Contrix/VUT_FIT_BP/documentation/obrazky-figures/esp8266.pdf

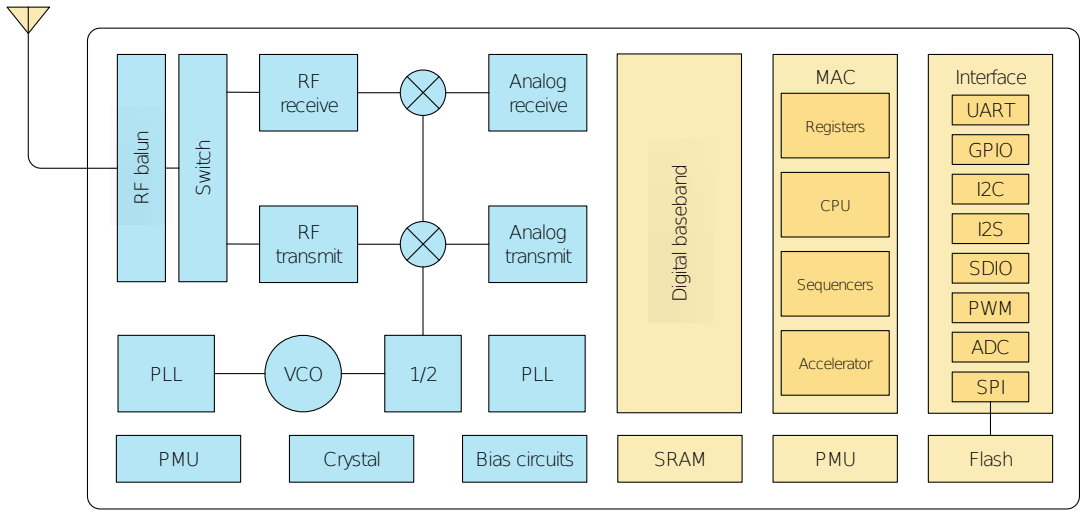
[picture p1: figure]
RF balun; Switch; RF receive; RF transmit; Analog receive; Analog transmit; PLL; VCO; Digital baseband; MAC; Interface; PMU; Crystal; Bias circuits; SRAM; SDIO; PWM; ADC; SPI; UART; GPIO; Flash; Registers; CPU; Sequencers; Accelerator
