Contrix/VUT_FIT_BP/documentation/obrazky-figures/cubemx.pdf

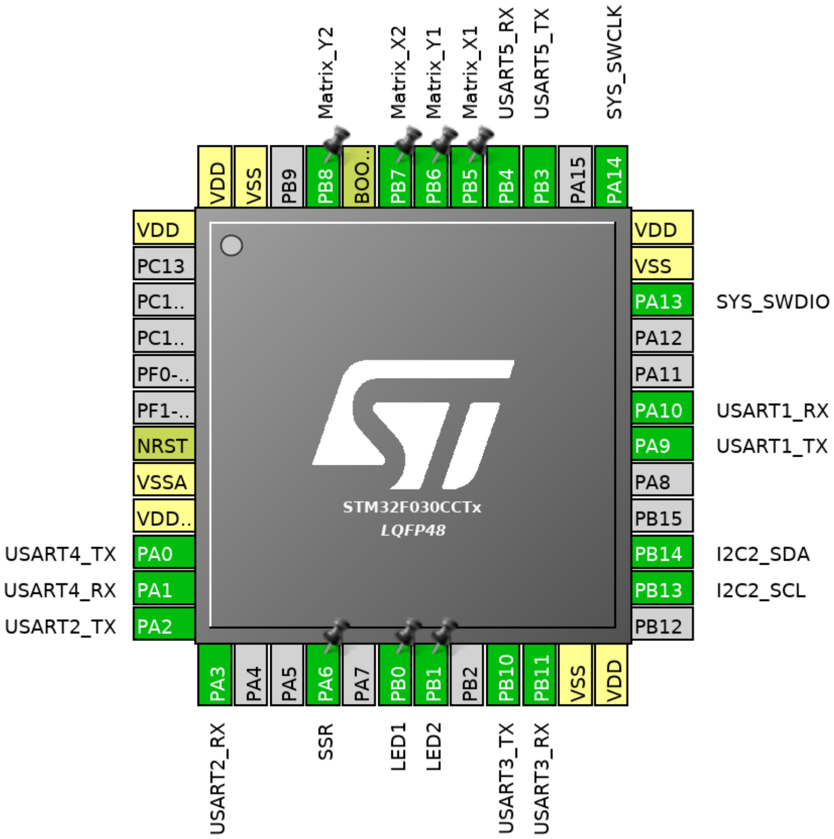
[picture p5: page 1]
