Contrix/VUT_FIT_BP/documentation/obrazky-figures/float.pdf

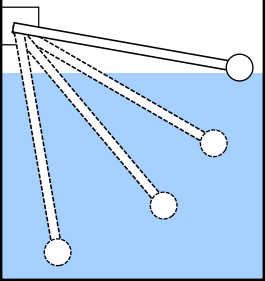
[picture p6: figure]
