Contrix/VUT_FIT_BP/documentation/obrazky-figures/jsn.pdf

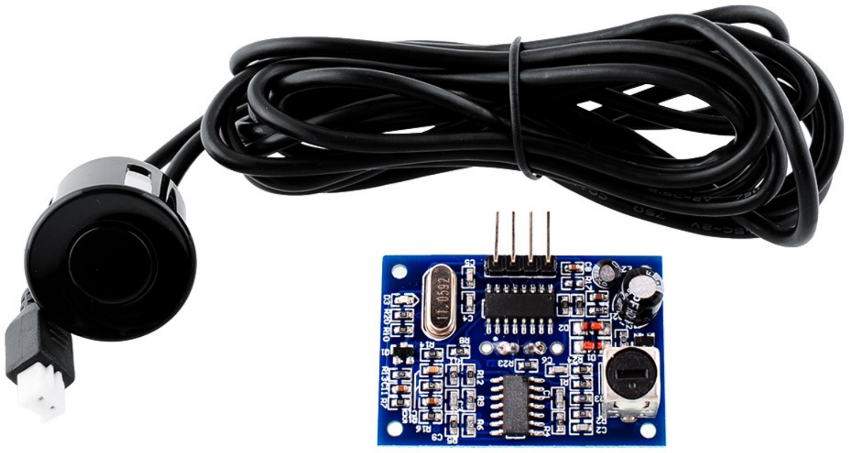
[picture p7: page 1]
