Contrix/VUT_FIT_BP/documentation/obrazky-figures/jsn_mes.pdf

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

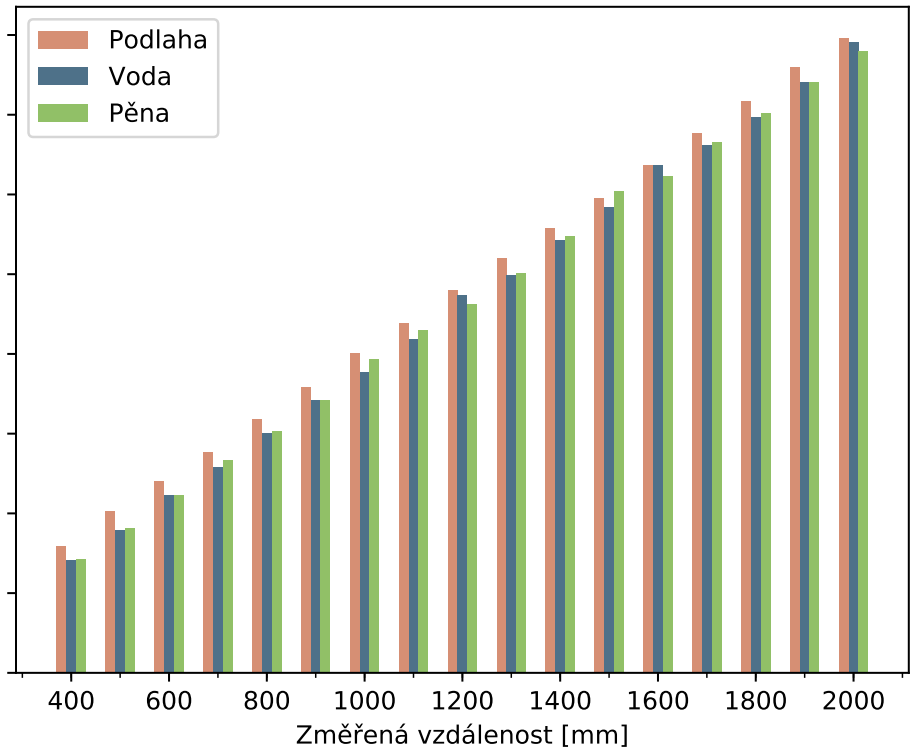
[picture p8: figure]
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
