Contrix/VUT_FIT_BP/documentation/obrazky-figures/lidar.pdf

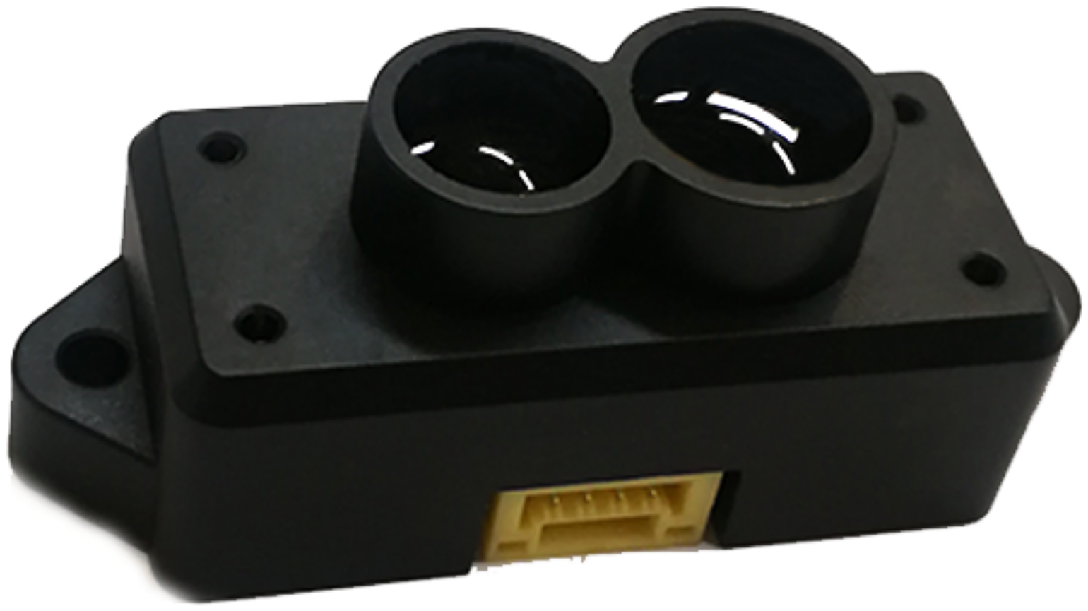
[picture p9: page 1]
