Contrix/VUT_FIT_BP/documentation/obrazky-figures/lidar_mes.pdf

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

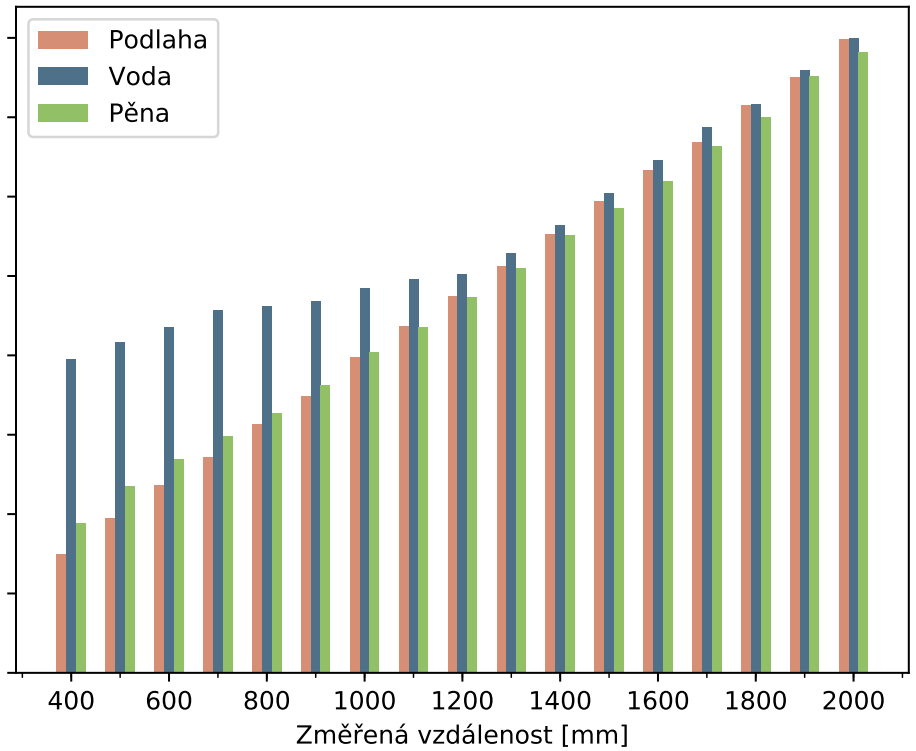
[picture p10: figure]
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
