Contrix/VUT_FIT_BP/documentation/obrazky-figures/main_board_3D.pdf

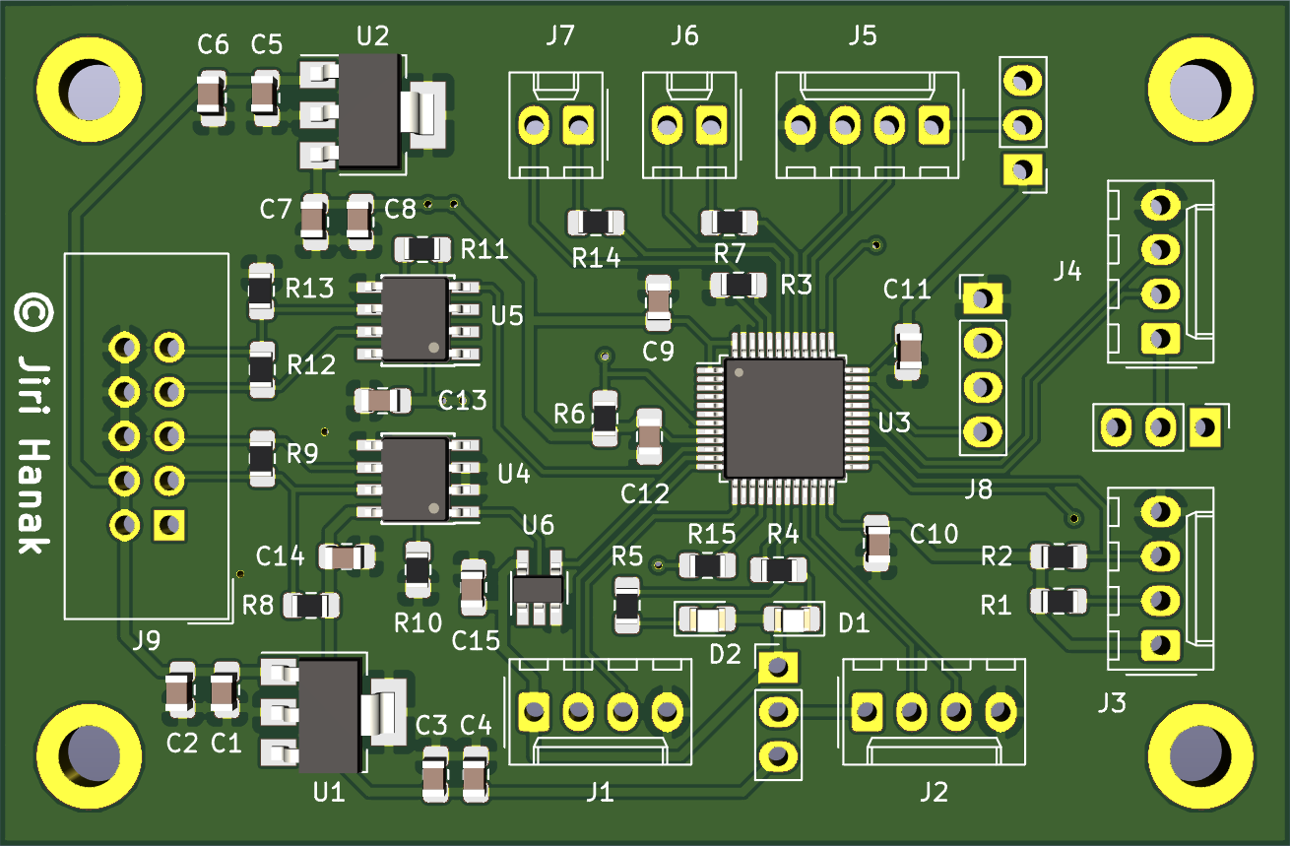
[picture p11: page 1]
