Contrix/VUT_FIT_BP/documentation/obrazky-figures/mcp.pdf

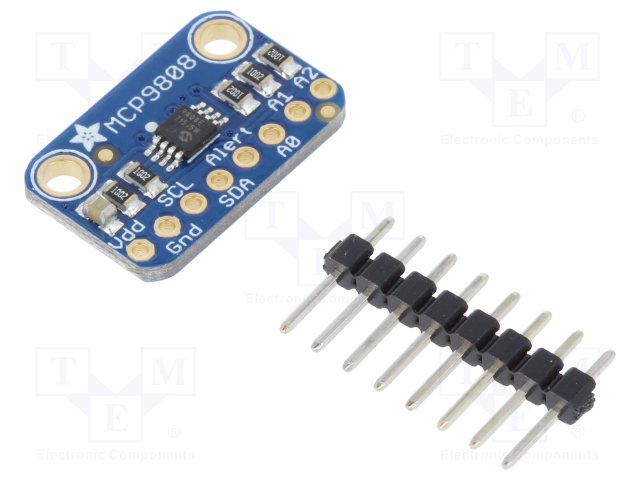
[picture p12: page 1]
