Contrix/VUT_FIT_BP/documentation/obrazky-figures/pk.pdf

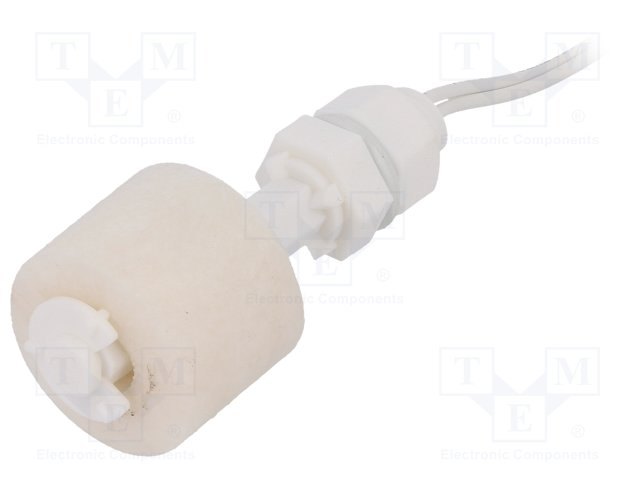
[picture p13: page 1]
