Contrix/VUT_FIT_BP/documentation/obrazky-figures/support_board_3D.pdf

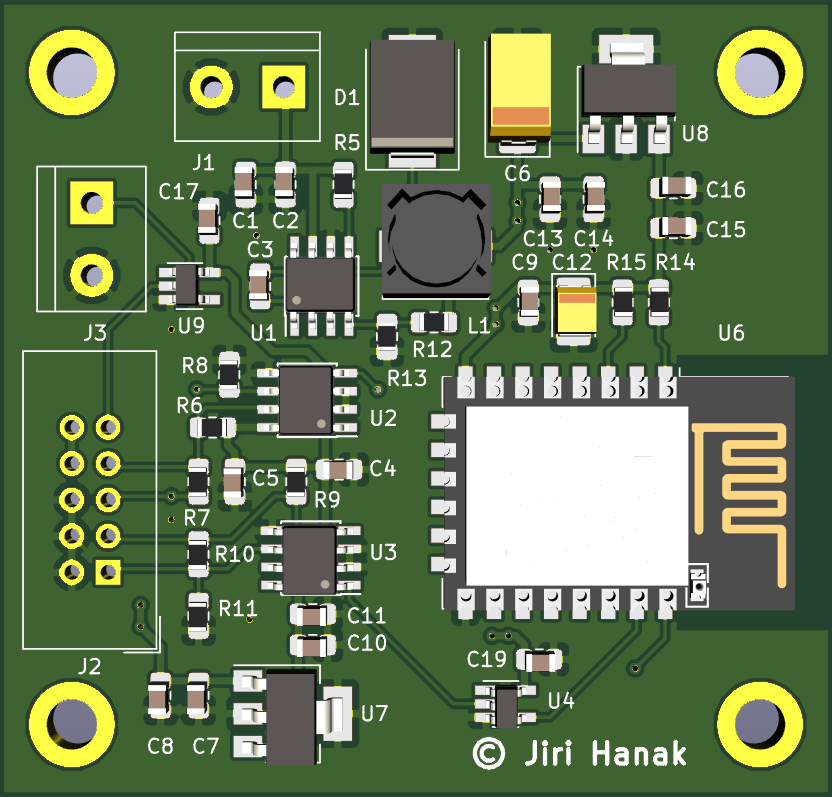
[picture p14: page 1]
