Contrix/VUT_FIT_BP/documentation/obrazky-figures/main_board_scheme.pdf

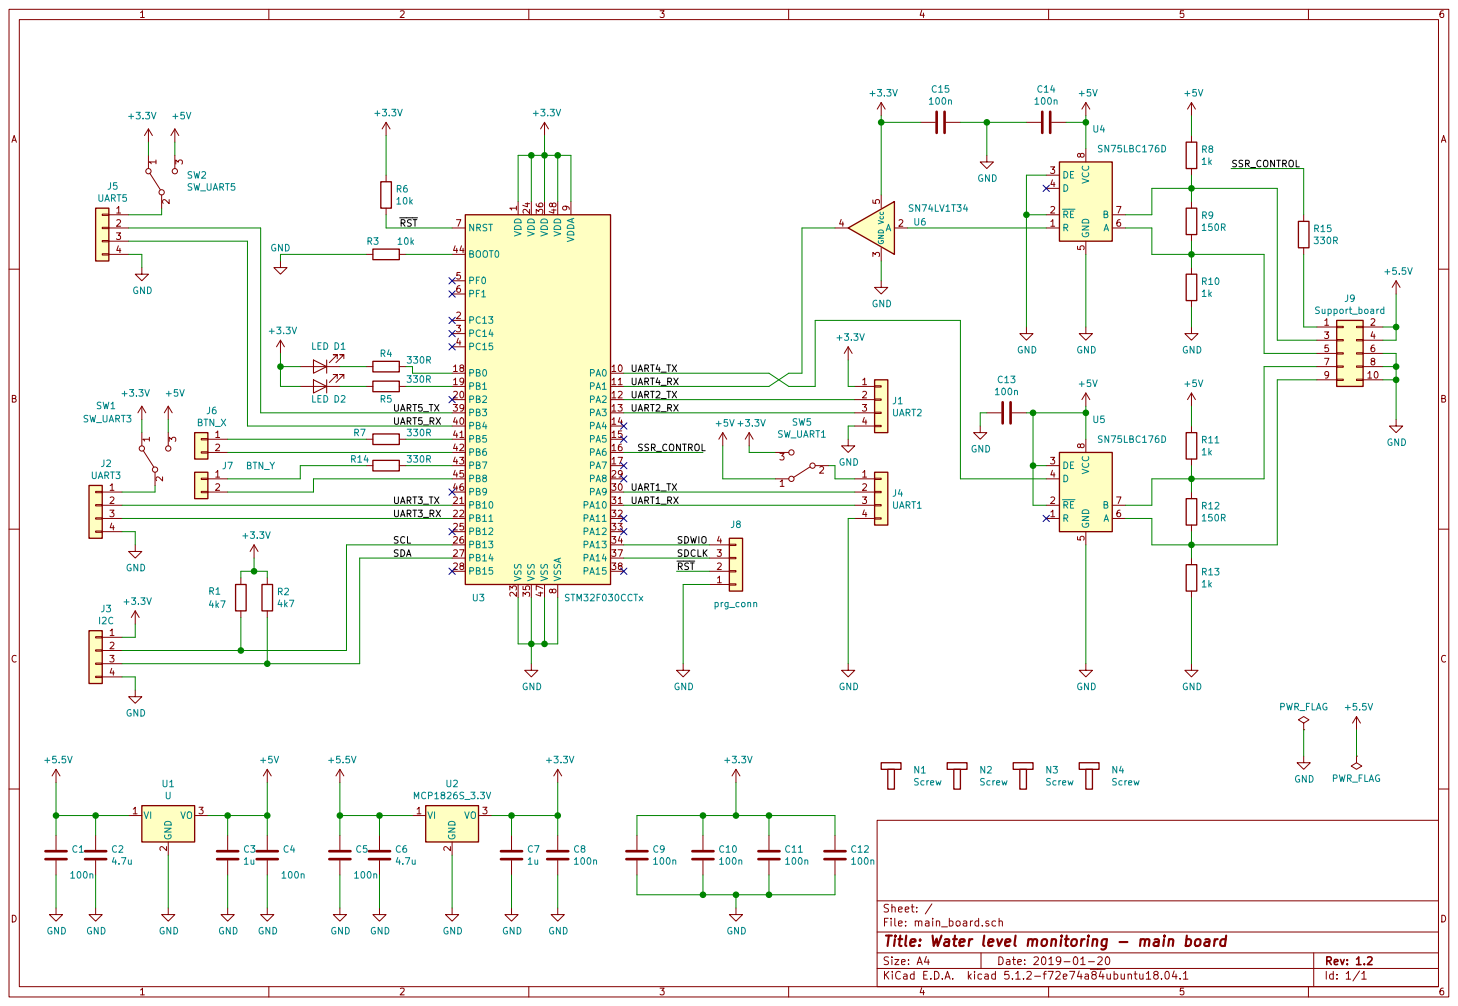
[picture p20: page 1]

1 VDD 24 VDD 36 VDD 48 VDDA

9 VSS 23 VSS 35 VSS 47 VSSA

File: main_board.sch Sheet: /
Id: 1/1 Title: Water level monitoring - main board
