Contrix/VUT_FIT_BP/documentation/obrazky-figures/support_board_scheme.pdf

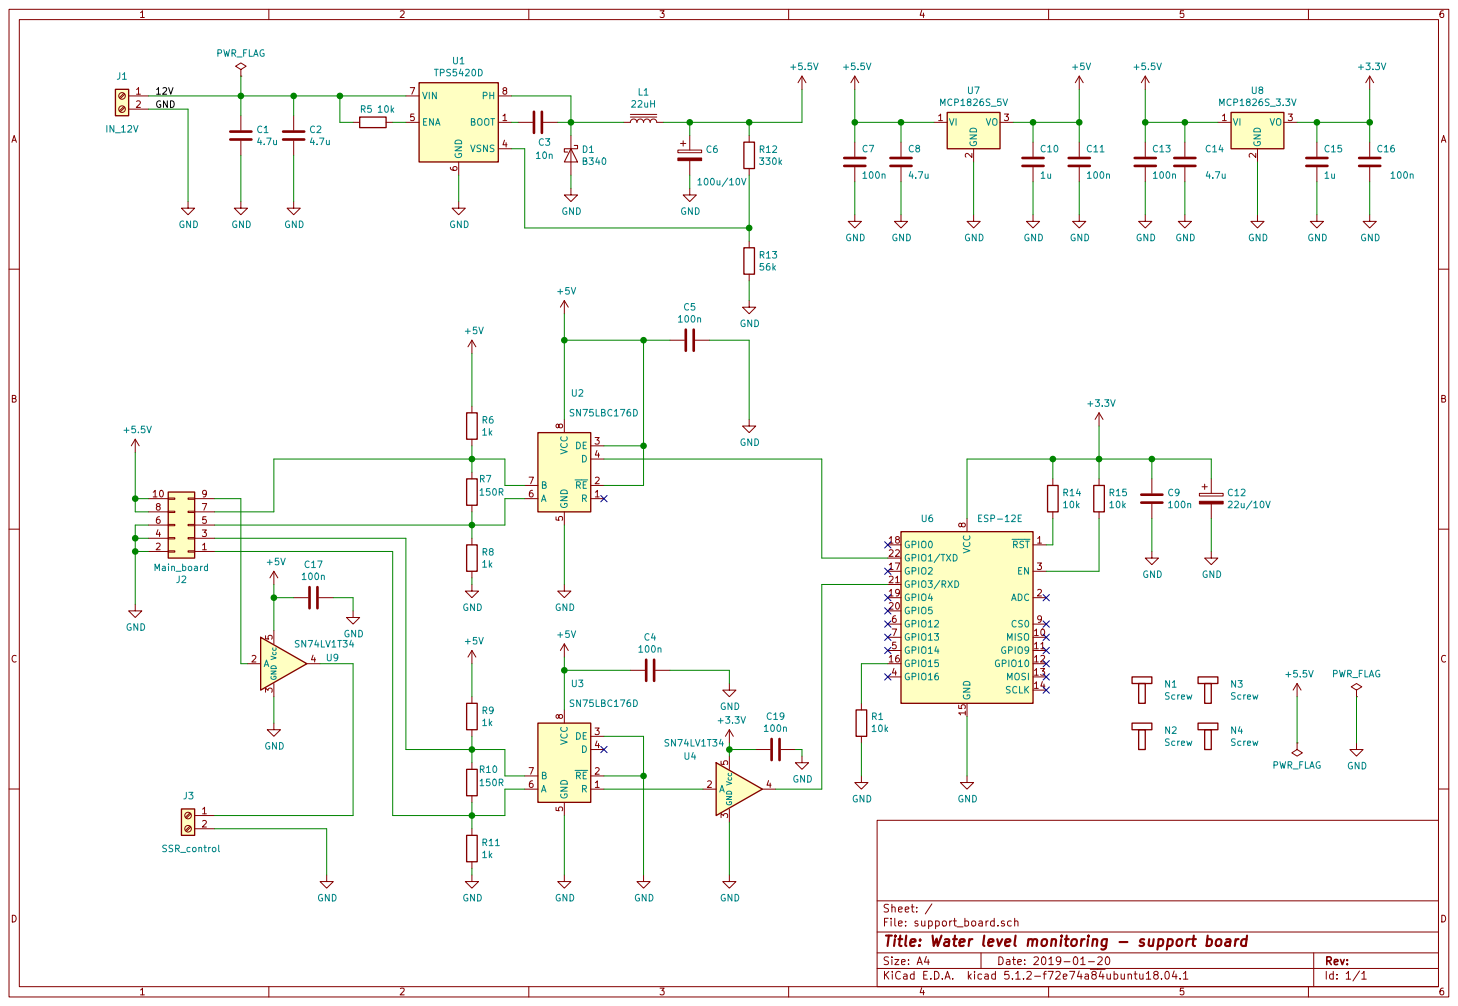
[picture p21: page 1]

6 VIN 7 PH 8 U1 TPS5420D GND GND
4.7u GND

File: support_board.sch Sheet: /
Id: 1/1 Title: Water level monitoring - support board
