Contrix/VUT_FIT_BP/documentation/obrazky-figures/diagram.pdf

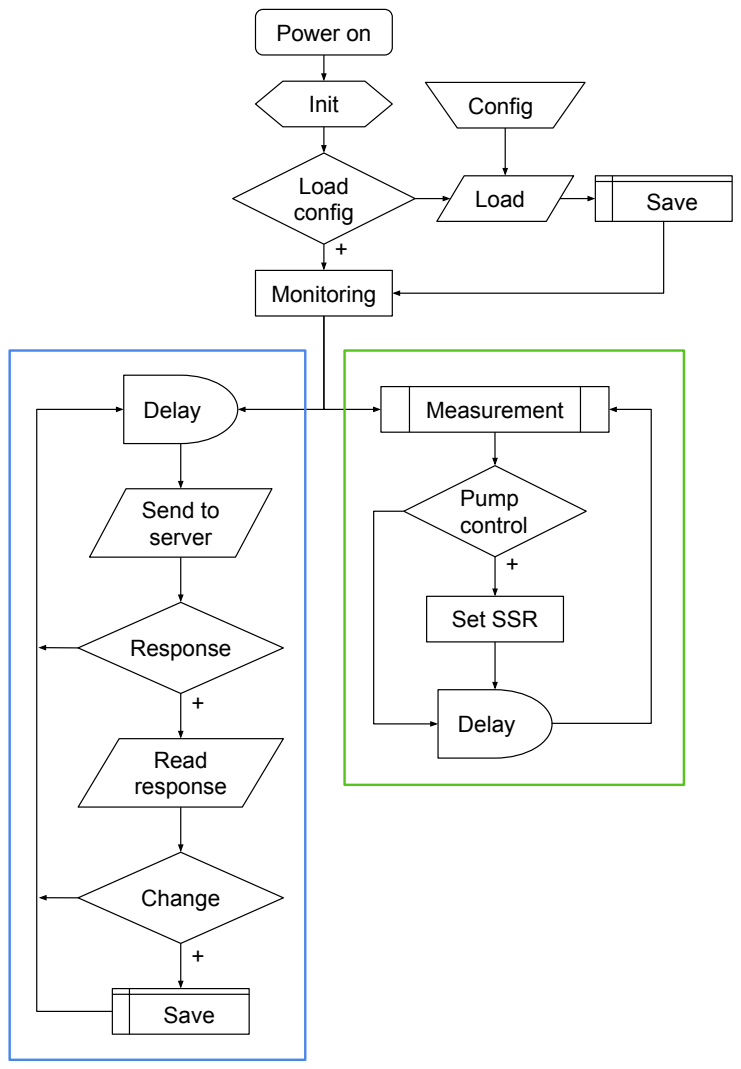
[picture p22: page 1]
Power on; Load config; Init; Load; Measurement; Save; Delay; Pump control; Send to server; Read response; Change; Monitoring; Set SSR; Config; Response
