Contrix/VUT_FIT_BP/documentation/obrazky-figures/scheme.pdf

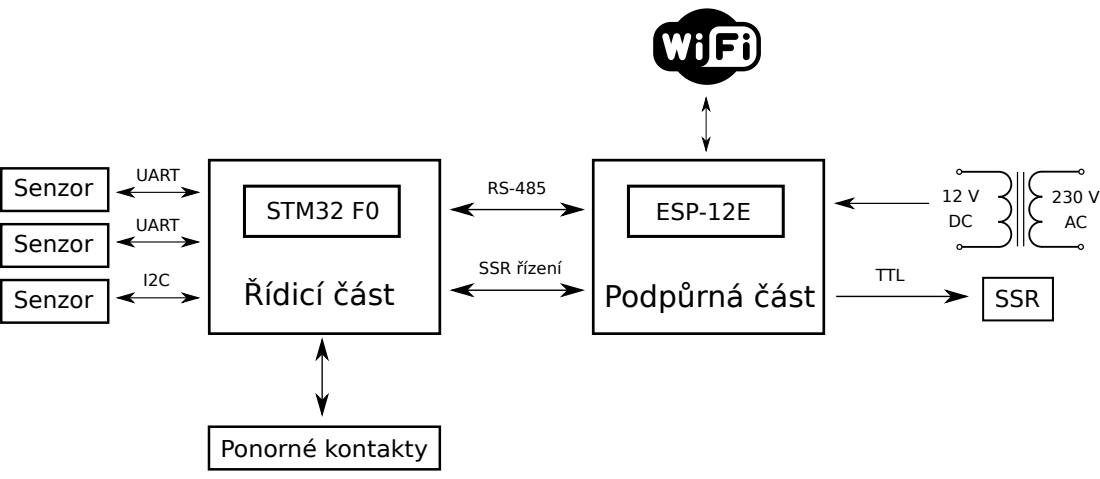
[picture p23: page 1]
Řídicí část; Podpůrná část; UART; Senzor; ESP-12E; 12 V DC STM32 F0; SSR; Ponorné kontakty

TTL SSR řízení
