Contrix/VUT_FIT_BP/hardware/support_board/gerber/support_board-F.Mask.pdf

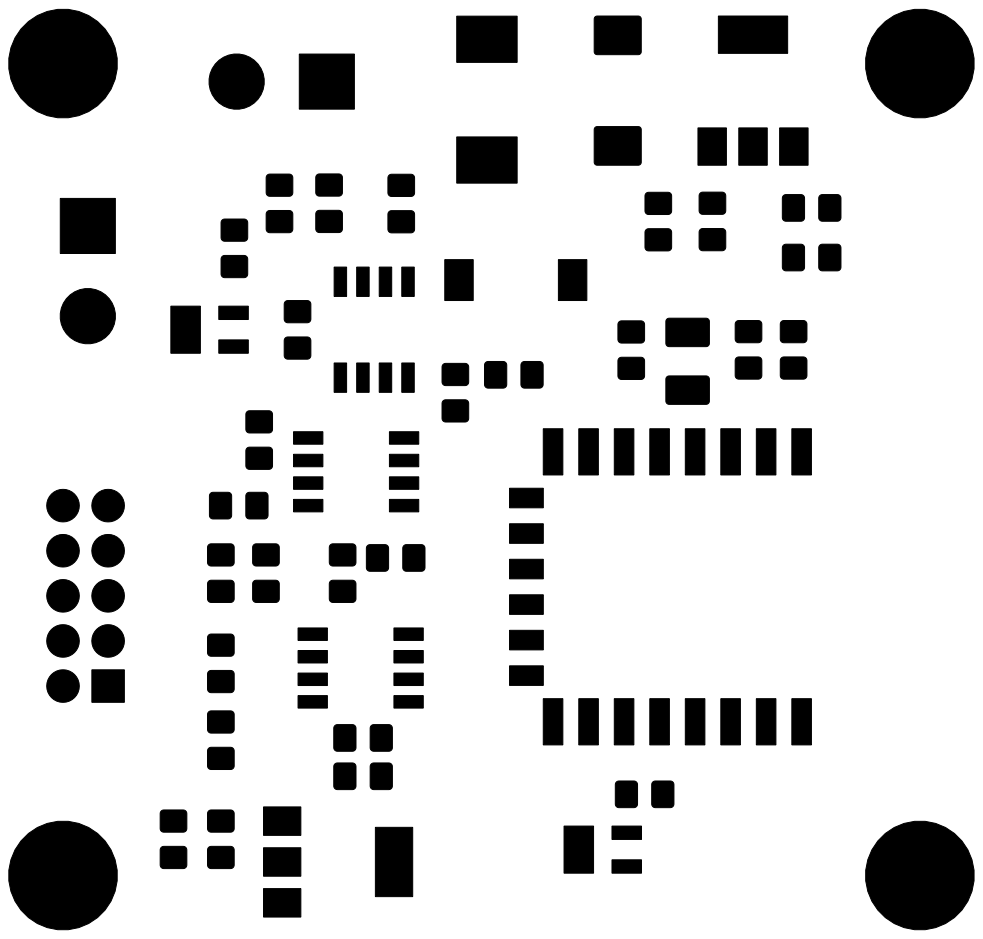
[picture p33: page 1]
