Contrix/VUT_FIT_BP/hardware/support_board/gerber/support_board-F.SilkS.pdf

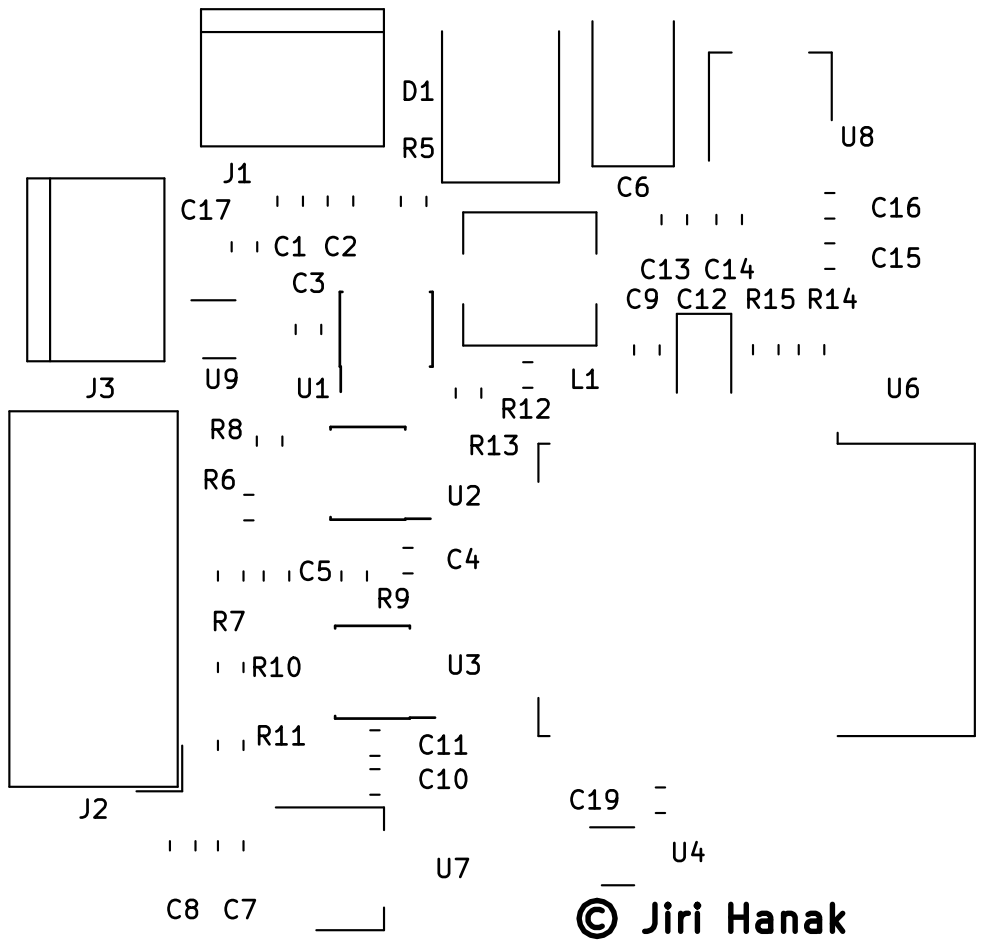
[picture p34: page 1]
