Contrix/VUT_FIT_BP/documentation/obrazky-figures/main_board_pcb.pdf

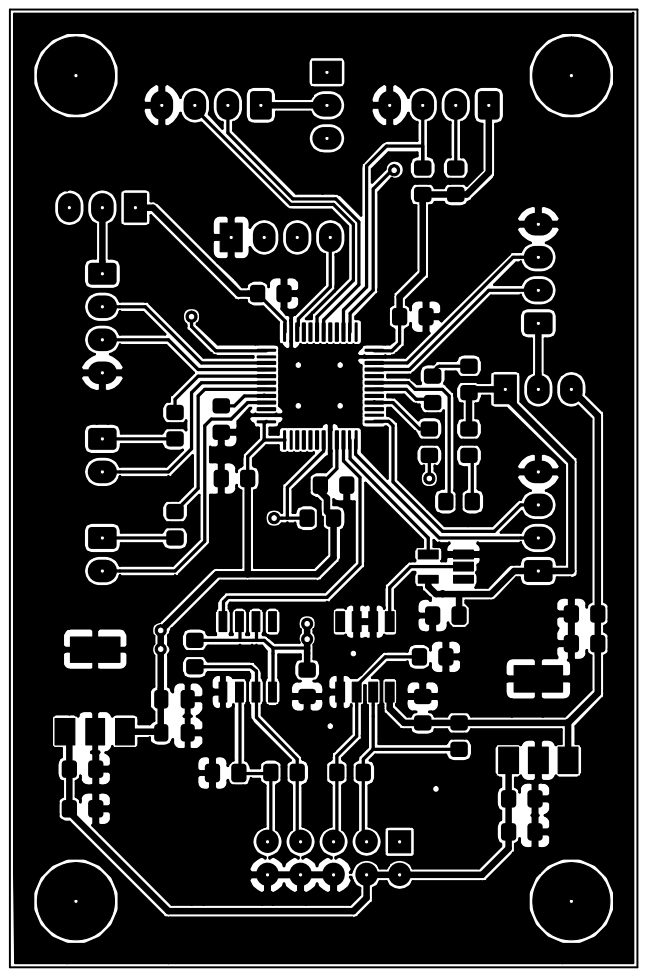
[picture p35: page 1]

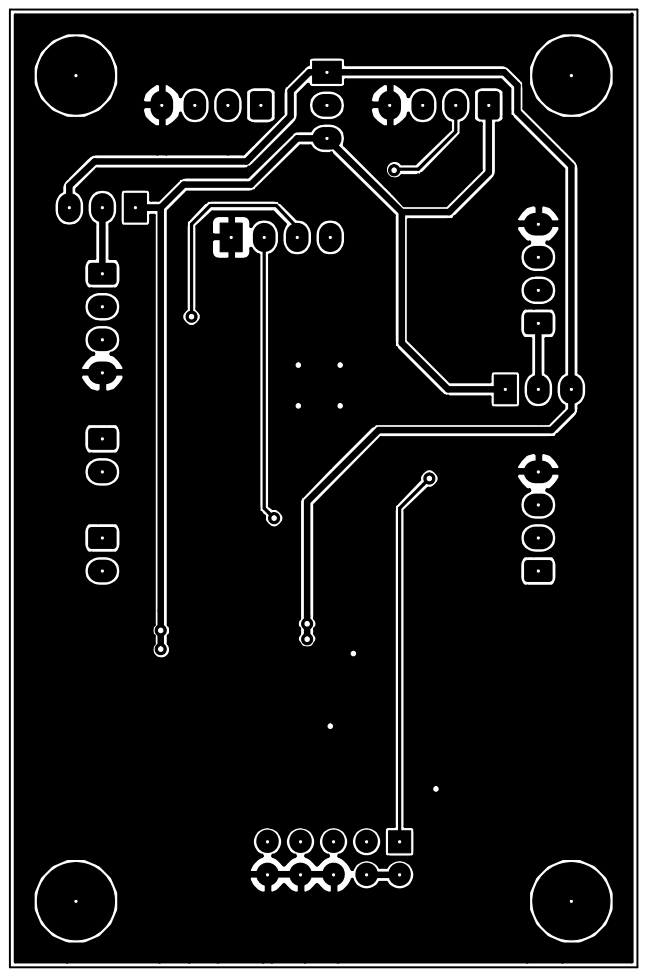
[picture p36: page 2]
