Contrix/VUT_FIT_BP/documentation/obrazky-figures/support_board_pcb.pdf

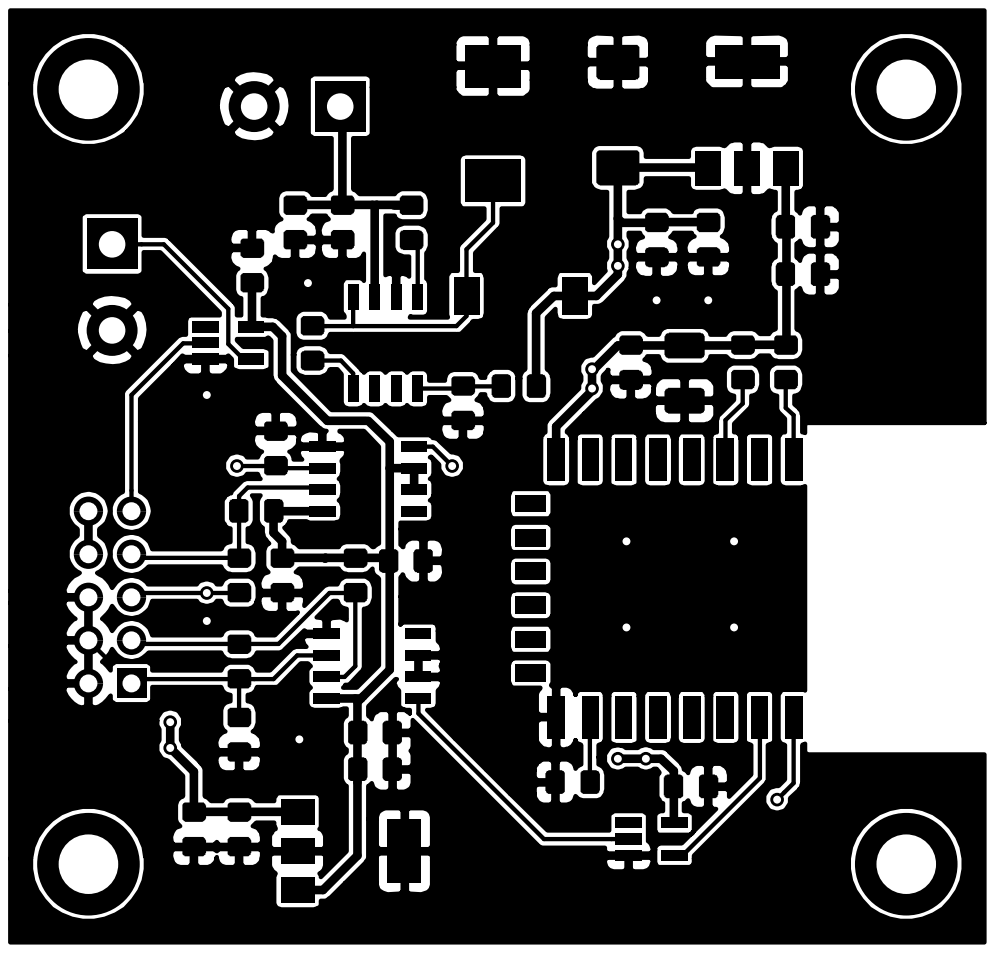
[picture p37: page 1]

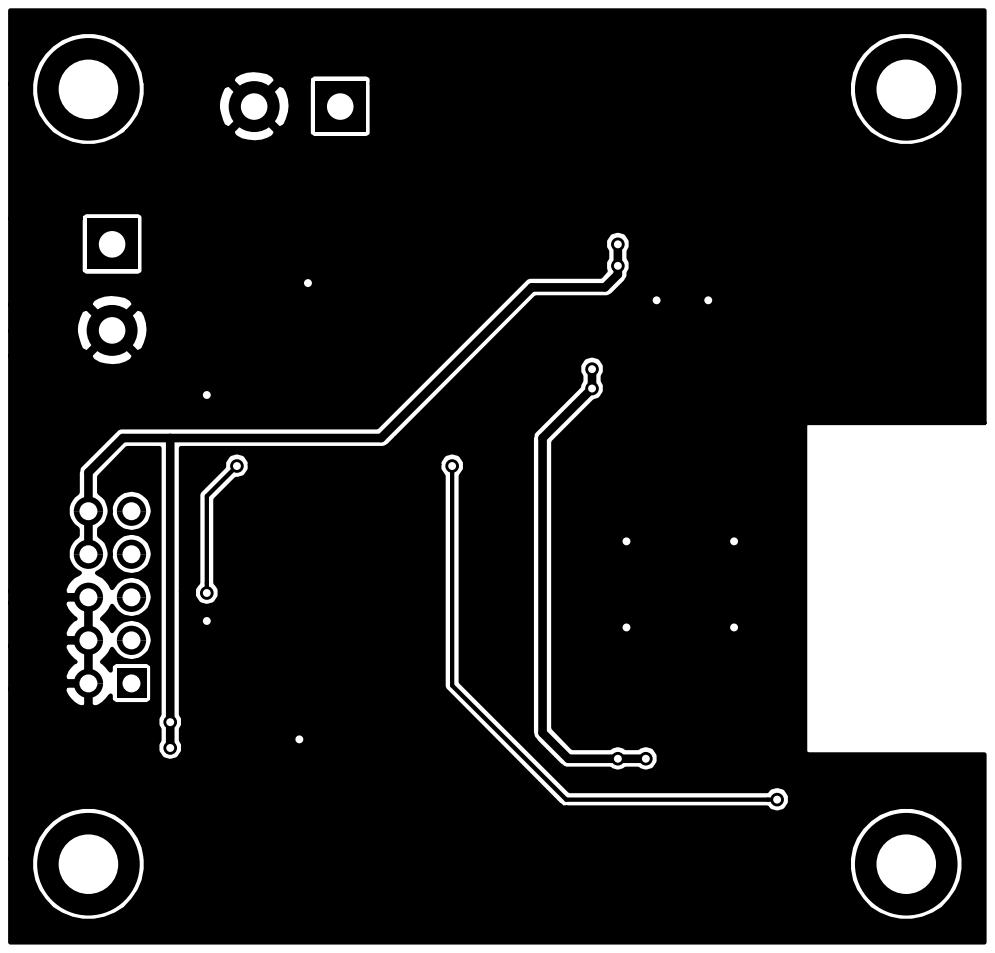
[picture p38: page 2]
