Contrix/VUT_FIT_BP/documentation/obrazky-figures/matrix.pdf

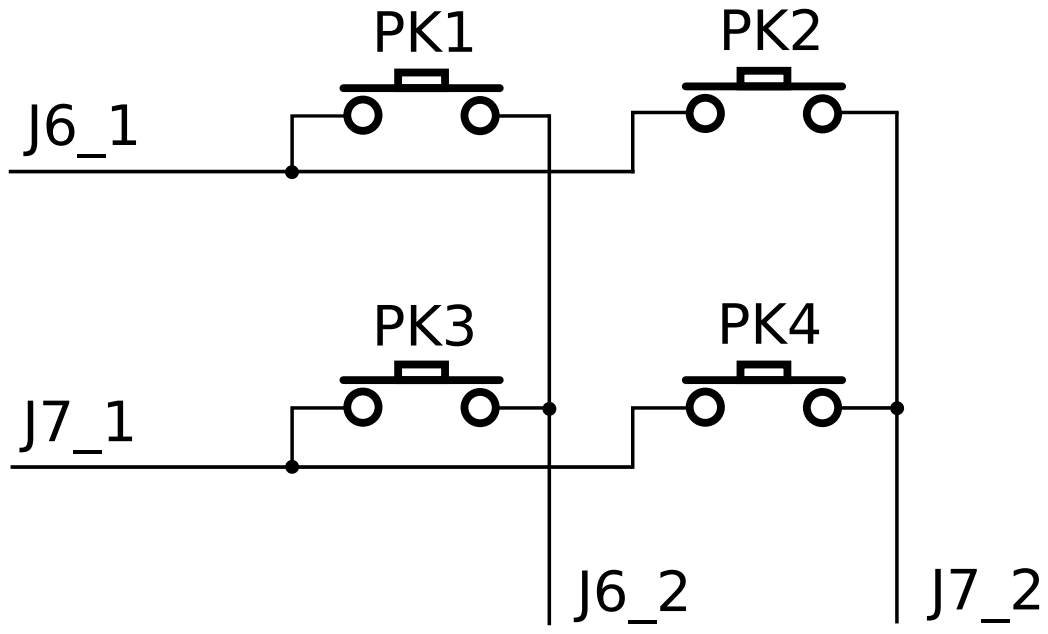
[picture p39: page 1]
