Contrix/VUT_FIT_BP/documentation/obrazky-figures/system.pdf

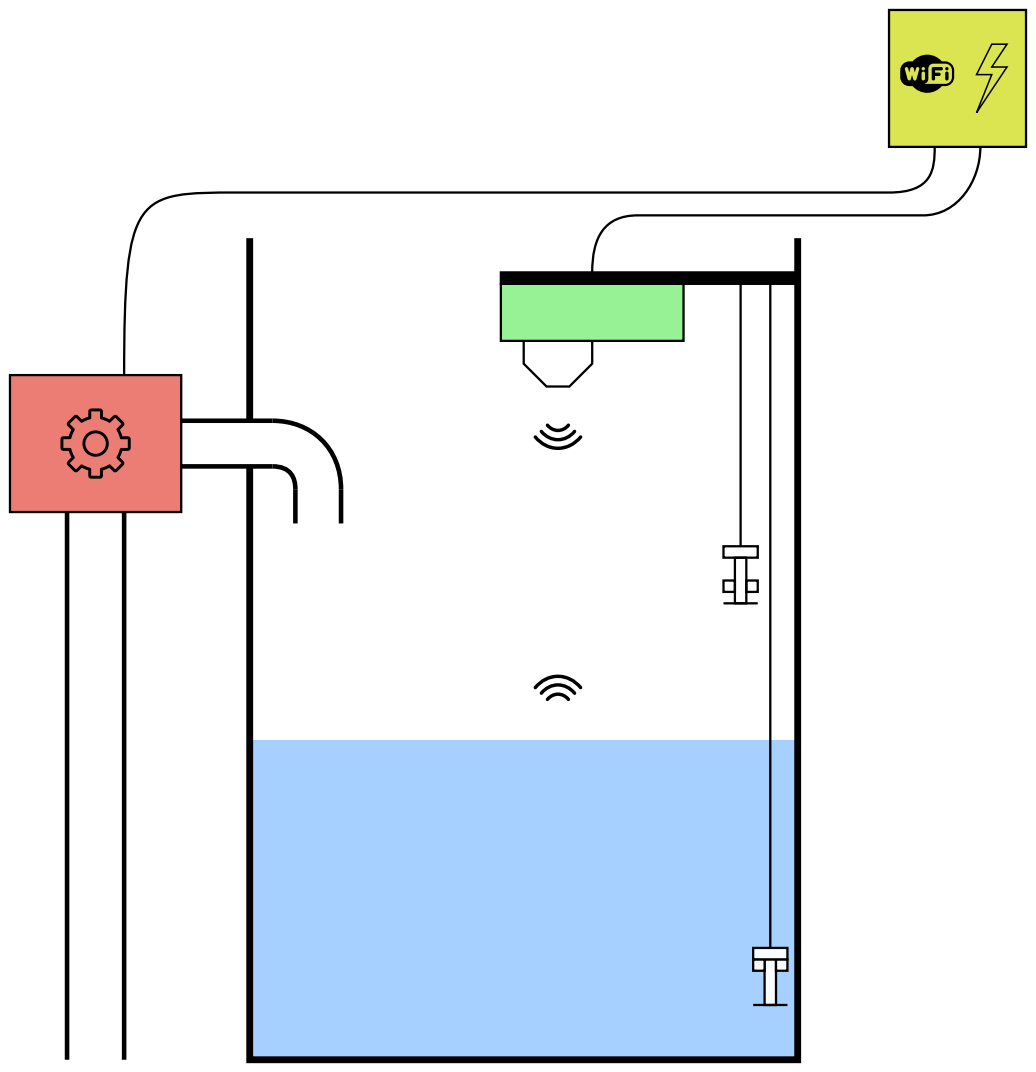
[picture p40: page 1]
