Contrix/VUT_FIT_BP/firmware/Inc/embd_sys_i2c.h

/**
 * Water level monitoring
 * I2C module
 * @Author HanakJiri, xhanak33
 * @file embd_sys_i2c.h
 */

#ifndef WATER_MONITORING_EMBD_SYS_I2C_H
#define WATER_MONITORING_EMBD_SYS_I2C_H

#include "../Drivers/CMSIS/Device/ST/STM32F0xx/Include/stm32f030xc.h"
#include "../Drivers/STM32F0xx_HAL_Driver/Inc/stm32f0xx_hal.h"
#include "../Drivers/STM32F0xx_HAL_Driver/Inc/stm32f0xx_hal_i2c.h"

I2C_HandleTypeDef hi2c2;
#endif //WATER_MONITORING_EMBD_SYS_I2C_H
