Contrix/VUT_FIT_BP/firmware/Src/embd_sys_i2c.c

/**
 * Water level monitoring
 * I2C module
 * @Author HanakJiri, xhanak33
 * @file embd_sys_i2c.c
 */

#include "../Inc/embd_sys_i2c.h"

void HAL_I2C_MasterTxCpltCallback(I2C_HandleTypeDef *hi2c) {

}

void HAL_I2C_MasterRxCpltCallback(I2C_HandleTypeDef *hi2c) {

}
